fxkuehl/mantis/assets/640/v0.3-mantis_bare.jpg

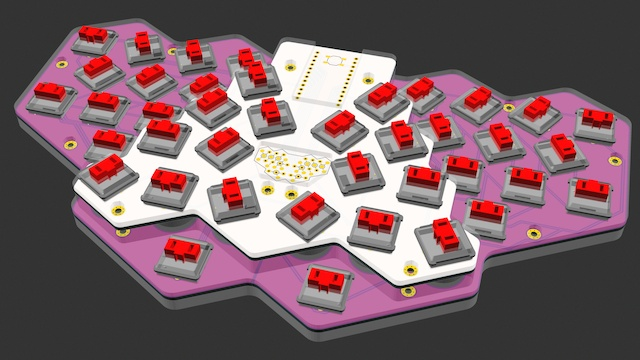
assets/640/v0.3-mantis_bare.jpg
