fxkuehl/mantis/assets/640/v0.3-mantis_naked.jpg

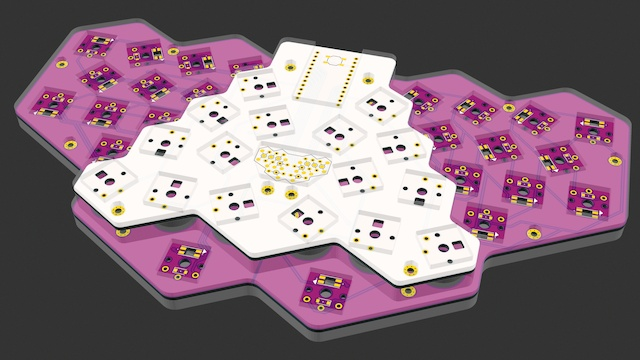
assets/640/v0.3-mantis_naked.jpg
