fxkuehl/mantis/assets/640/v0.3-mantis_top.jpg

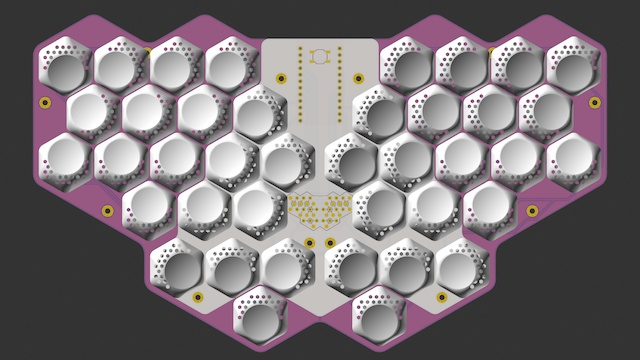
assets/640/v0.3-mantis_top.jpg
