fxkuehl/mantis/assets/mantis-v0.3-leds.jpg

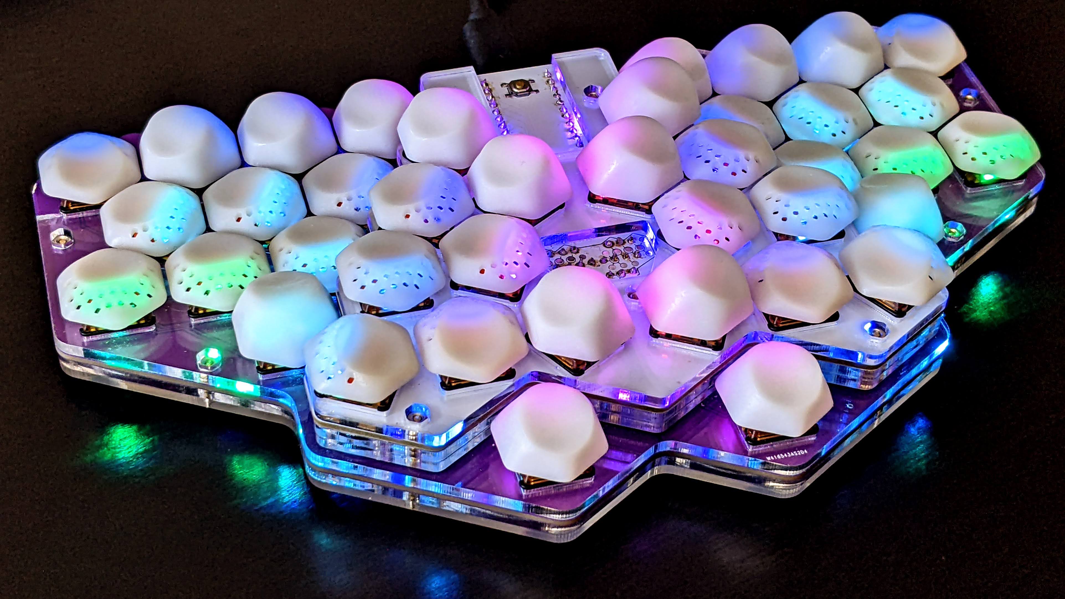
assets/mantis-v0.3-leds.jpg
