fxkuehl/mantis/assets/v0.3-photos/01-mantis-rgb-top.jpg

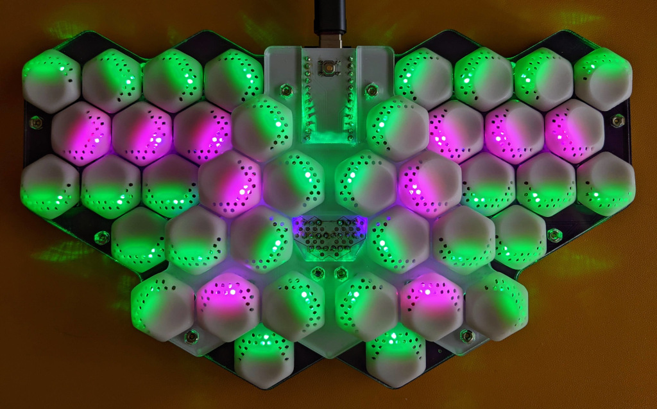
assets/v0.3-photos/01-mantis-rgb-top.jpg
