fxkuehl/mantis/keycap/raised_outline.dxf

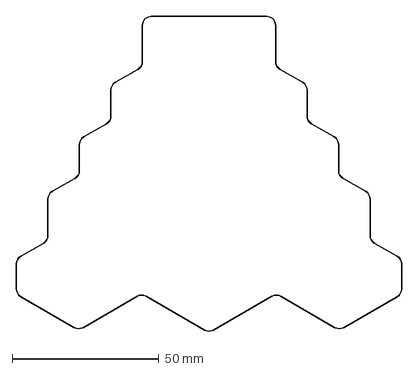
[picture p27: CAD file, 2023-06-12]
keycap/raised_outline.dxf
131.5 x 107.6 mm
