fxkuehl/mantis/keycap/raised.dxf

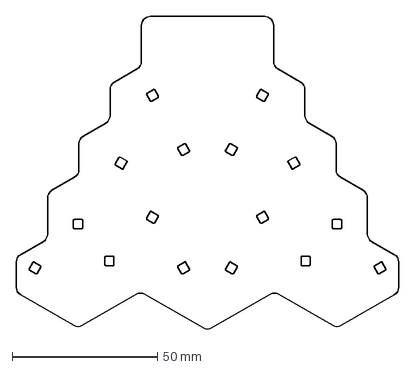
[picture p28: CAD file, 2023-06-12]
keycap/raised.dxf
131.5 x 107.6 mm
