fxkuehl/mantis/keycap/deprecated/keycap-v2-28.stl

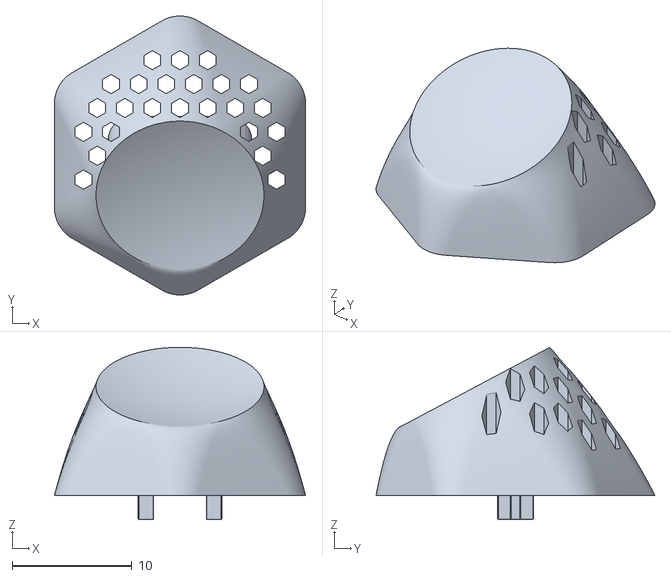
[picture p29: CAD file, 2023-09-19, an earlier design]
keycap/deprecated/keycap-v2-28.stl
21.0 x 23.3 x 14.4
